a-bernard1/tank_app/electronics/PCB_alim_miniChar.kicad_sch

## KiCad design electronics/PCB_alim_miniChar.kicad_sch (2026-10-07)

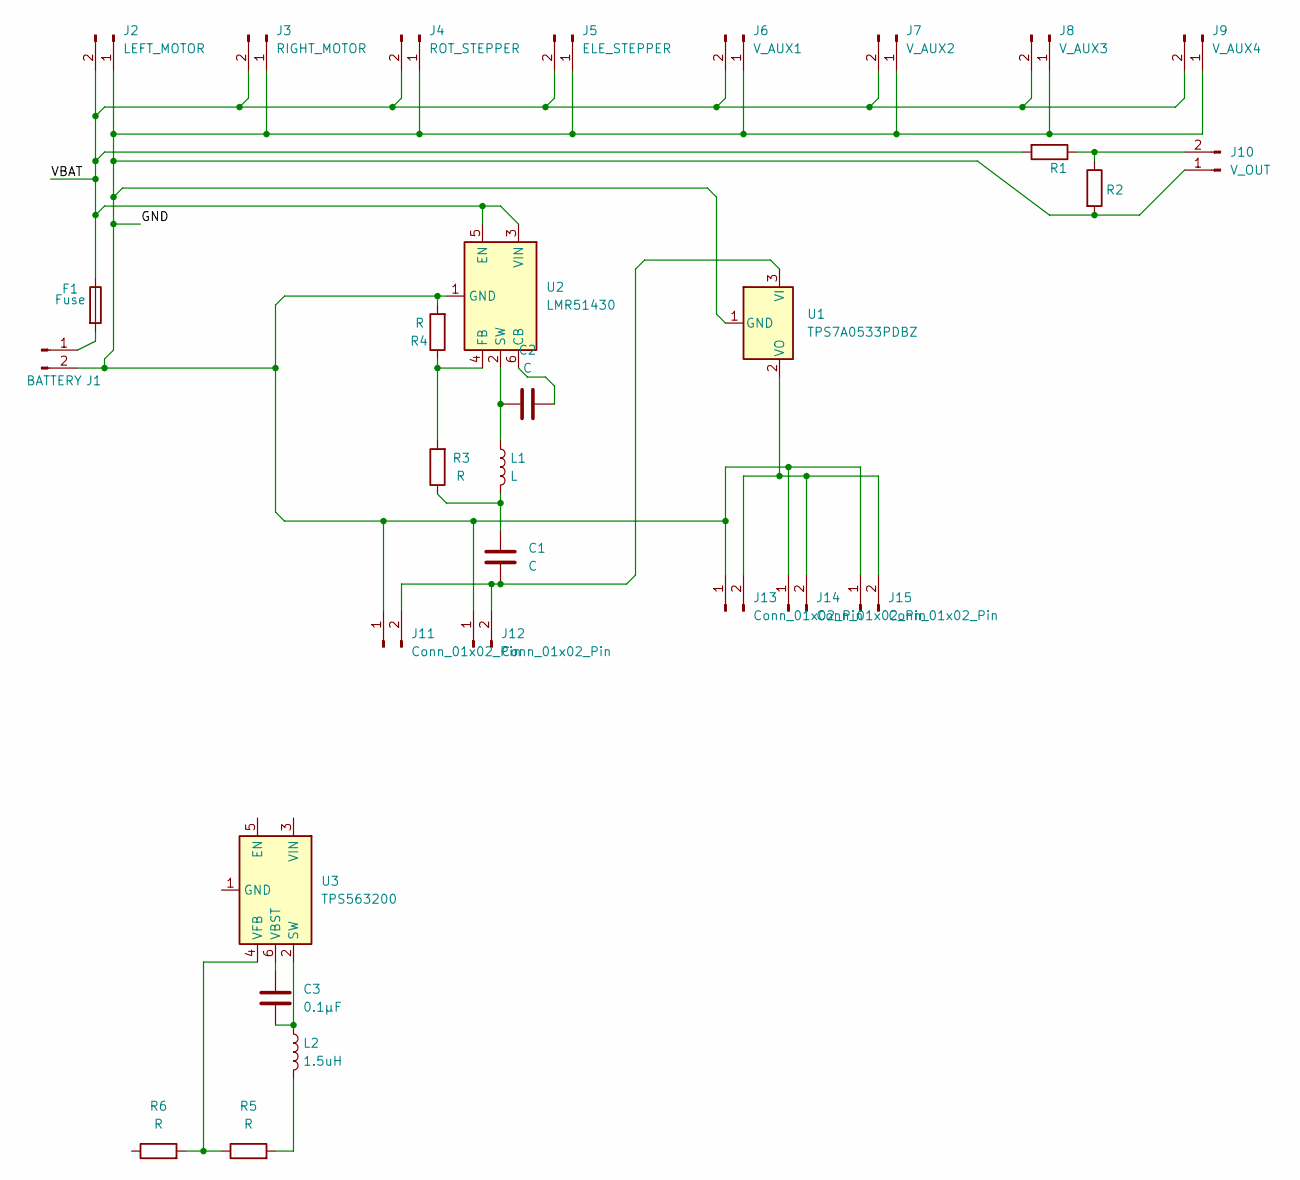
[picture p13: schematic PCB_alim_miniChar.kicad_sch]

Parts:
C1, C2: C; SOIC-8_3.9x4.9mm_P1.27mm
C3: 0.1µF; PLCC-44_16.6x16.6mm_P1.27mm
F1: Fuse
J1: BATTERY
J2: LEFT_MOTOR
J3: RIGHT_MOTOR
J4: ROT_STEPPER
J5: ELE_STEPPER
J6: V_AUX1
J7: V_AUX2
J8: V_AUX3
J9: V_AUX4
J10: V_OUT
J11: Conn_01x02_Pin; SOT-23
J12, J13, J14, J15: Conn_01x02_Pin
L1: L
L2: 1.5uH; Relay_DPDT_Finder_30.22
R1, R3: R; DIP-8_W7.62mm
R2, R4, R5, R6: R
U1: TPS7A0533PDBZ; SOT-23
U2: LMR51430; SOT-23-6
U3: TPS563200; SOT-23-6

Connections:
GND: J1.2, J2.1, J3.1, J4.1, J5.1, J6.1, J7.1, J8.1, J9.1, J10.1, J11.1, J12.1, J13.1, J14.1, J15.1, R2.2, R4.2, U1.1 (GND), U2.1 (GND)
unnamed: C1.1, L1.2, R3.1
unnamed: C1.2, J11.2, J12.2, U1.3 (VI)
unnamed: C2.1, L1.1, U2.2 (SW)
unnamed: C2.2, U2.6 (CB)
unnamed: C3.1, U3.6 (VBST)
unnamed: C3.2, L2.1, U3.2 (SW)
unnamed: F1.2, J1.1
unnamed: J10.2, R1.1, R2.1
unnamed: J13.2, J14.2, J15.2, U1.2 (VO)
unnamed: L2.2, R5.2
unnamed: R3.2, R4.1, U2.4 (FB)
unnamed: R5.1, R6.2, U3.4 (VFB)
VBAT: F1.1, J2.2, J3.2, J4.2, J5.2, J6.2, J7.2, J8.2, J9.2, R1.2, U2.3 (VIN), U2.5 (EN)
