a-bernard1/tank_app/arduino_tank_code/chassis_arduino_project/src/Motor.hpp

#ifndef DEF_MOTOR
#define DEF_MOTOR

#include <cstdint>
#include <Arduino.h>

class Motor{
    private:
        uint8_t pwmForward;
        uint8_t pwmBackward;
        uint8_t enable1;
        uint8_t enable2;
        uint8_t state;
        uint8_t currentSpeed;
        unsigned long lastBrakeTime = 0;
        uint8_t targetSpeed = 0;
        uint8_t targetState = 0;
        bool isBraking = false;

    public:
        Motor(uint8_t fwd, uint8_t back, uint8_t en1, uint8_t en2);

        void begin();

        void forward(uint8_t speed);

        void backward(uint8_t speed);

        void stop();

        void updateBrake();
};


#endif
